d-ronin/openlager/shared/diskio.c

/*-----------------------------------------------------------------------*/
/* Low level disk I/O module skeleton for FatFs     (C)ChaN, 2016        */
/*-----------------------------------------------------------------------*/

#include "diskio.h"             /* FatFs lower layer API */
#include <sdio.h>               /* dRonin SDIO implementation functions */

/* Definitions of physical drive number for each drive */
#define CARD            0       /* Example: Map ATA harddisk to physical drive 0 */

/*-----------------------------------------------------------------------*/
/* Get Drive Status                                                      */
/*-----------------------------------------------------------------------*/

DSTATUS disk_status(
	BYTE pdrv               /* Physical drive nmuber to identify the drive */
	)
{
	if (pdrv != CARD)
		return STA_NOINIT;

	return 0;
}

/*-----------------------------------------------------------------------*/
/* Inidialize a Drive                                                    */
/*-----------------------------------------------------------------------*/

DSTATUS disk_initialize(
	BYTE pdrv                               /* Physical drive nmuber to identify the drive */
	)
{
	if (pdrv != CARD)
		return STA_NOINIT;

	return 0;
}

/*-----------------------------------------------------------------------*/
/* Read Sector(s)                                                        */
/*-----------------------------------------------------------------------*/

DRESULT disk_read(
	BYTE pdrv,              /* Physical drive nmuber to identify the drive */
	BYTE *buff,             /* Data buffer to store read data */
	DWORD sector,   /* Sector address in LBA */
	UINT count              /* Number of sectors to read */
	)
{
	if (pdrv != CARD)
		return RES_PARERR;

	BYTE *rptr = buff;

	for (UINT i = 0; i < count; i++) {
		int retries = 3;

retry:;
		int ret = sd_read(rptr, sector + i);

		if (ret) {
			if (retries--) {
				goto retry;
			}

			return RES_ERROR;
		}

		rptr += 512;
	}

	return RES_OK;
}

/*-----------------------------------------------------------------------*/
/* Write Sector(s)                                                       */
/*-----------------------------------------------------------------------*/

DRESULT disk_write(
	BYTE pdrv,                      /* Physical drive nmuber to identify the drive */
	const BYTE *buff,       /* Data to be written */
	DWORD sector,           /* Sector address in LBA */
	UINT count                      /* Number of sectors to write */
	)
{
	if (pdrv != CARD)
		return RES_PARERR;

	const BYTE *wptr = buff;

	/* never do more than 6144 bytes in a txn for now.
	 * This is enough to get a significant boost over doing 512 at a
	 * time, while not risking TOO much on a CRC error (1280us wiretime
	 * at 1bit, 320us at 4
	 */
	uint16_t writing = 12;

	for (UINT i = 0; i < count; i += writing) {
		int retries = 3;

		uint16_t left = count - i;

		if (writing > left) {
			writing = left;
		}

retry:;
		int ret = sd_write(wptr, sector + i, writing);

		if (ret) {
			if (retries--) {
				goto retry;
			}

			return RES_ERROR;
		}

		wptr += 512 * writing;
	}

	return RES_OK;
}

/*-----------------------------------------------------------------------*/
/* Miscellaneous Functions                                               */
/*-----------------------------------------------------------------------*/

DRESULT disk_ioctl(
	BYTE pdrv,              /* Physical drive nmuber (0..) */
	BYTE cmd,               /* Control code */
	void *buff              /* Buffer to send/receive control data */
	)
{
	if (pdrv != CARD)
		return RES_PARERR;

	if (cmd == CTRL_SYNC)
		return RES_OK;

	return RES_PARERR;
}
