d-ronin/openlager/inc/lagercfg.h

const 
unsigned char lager_cfg[] = {
  0x7b, 0x0a, 0x09, 0x22, 0x73, 0x74, 0x61, 0x72, 0x74, 0x75, 0x70, 0x4d,
  0x6f, 0x72, 0x73, 0x65, 0x22, 0x20, 0x3a, 0x20, 0x22, 0x22, 0x2c, 0x0a,
  0x09, 0x22, 0x75, 0x73, 0x65, 0x53, 0x50, 0x49, 0x22, 0x20, 0x3a, 0x20,
  0x66, 0x61, 0x6c, 0x73, 0x65, 0x2c, 0x0a, 0x09, 0x22, 0x62, 0x61, 0x75,
  0x64, 0x52, 0x61, 0x74, 0x65, 0x22, 0x20, 0x3a, 0x20, 0x32, 0x30, 0x30,
  0x30, 0x30, 0x30, 0x30, 0x2c, 0x0a, 0x09, 0x22, 0x70, 0x72, 0x65, 0x61,
  0x6c, 0x6c, 0x6f, 0x63, 0x42, 0x79, 0x74, 0x65, 0x73, 0x22, 0x20, 0x3a,
  0x20, 0x31, 0x30, 0x34, 0x38, 0x35, 0x37, 0x36, 0x30, 0x30, 0x2c, 0x0a,
  0x09, 0x22, 0x70, 0x72, 0x65, 0x61, 0x6c, 0x6c, 0x6f, 0x63, 0x47, 0x72,
  0x6f, 0x77, 0x22, 0x20, 0x3a, 0x20, 0x66, 0x61, 0x6c, 0x73, 0x65, 0x0a,
  0x7d, 0x0a
};
unsigned int lager_cfg_len = 122;
